SamGowland/Gowla-Macro-Boards/Images/avr.PNG

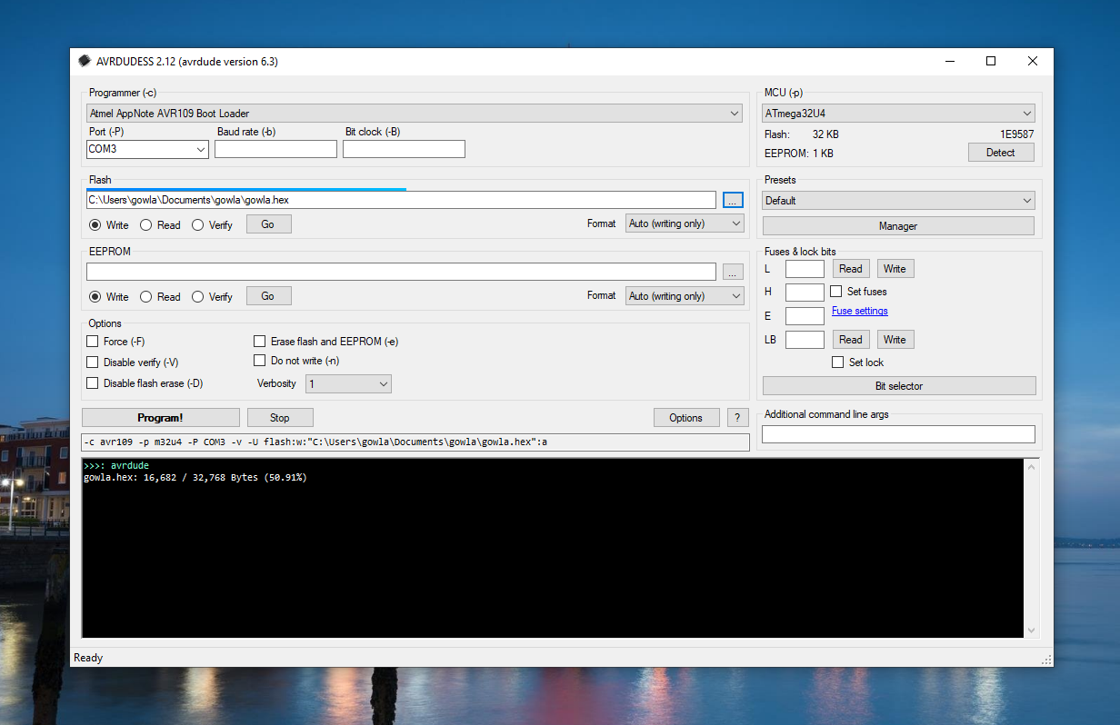
Images/avr.PNG
