SamGowland/Gowla-Macro-Boards/Images/black.PNG

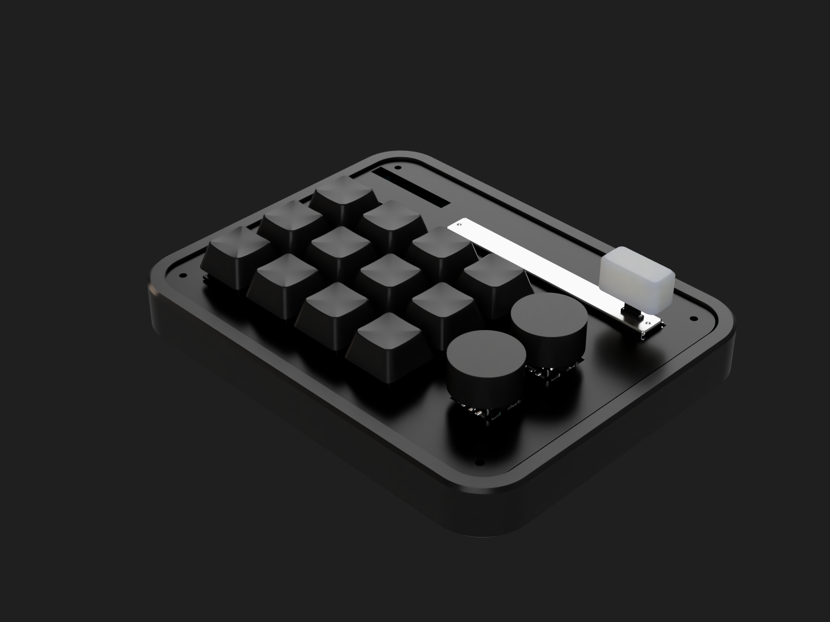
Images/black.PNG
