SamGowland/Gowla-Macro-Boards/Images/comp.jpg

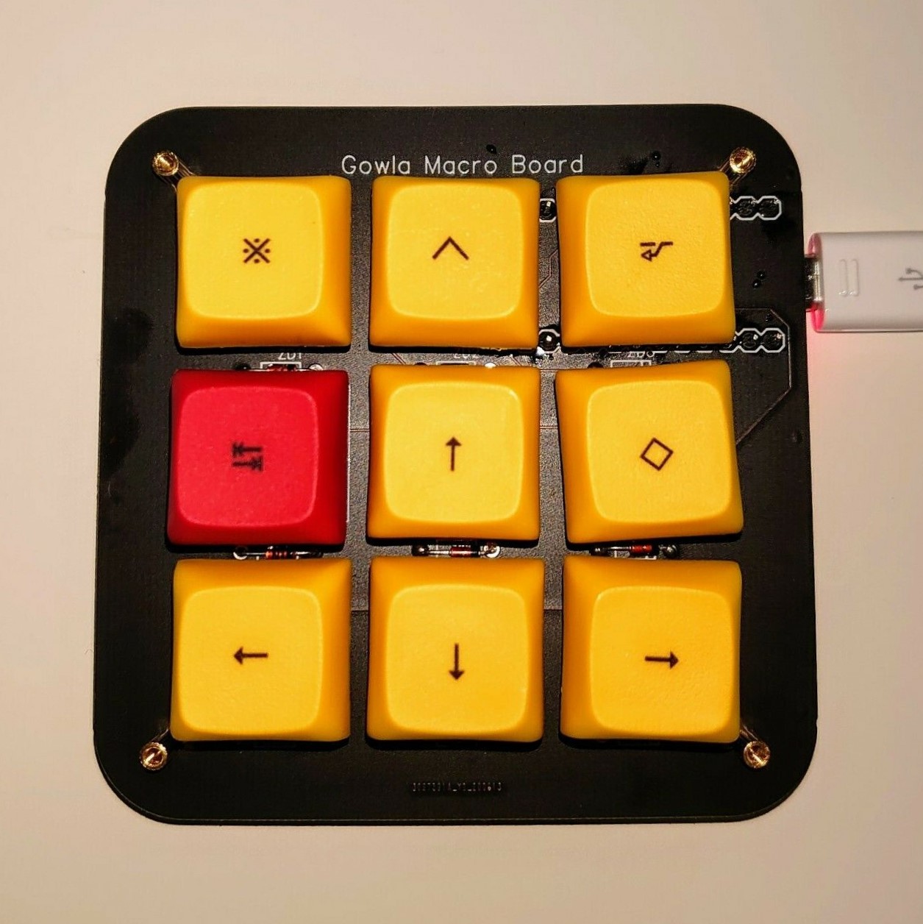
Images/comp.jpg
