SamGowland/Gowla-Macro-Boards/Images/eRGB back.PNG

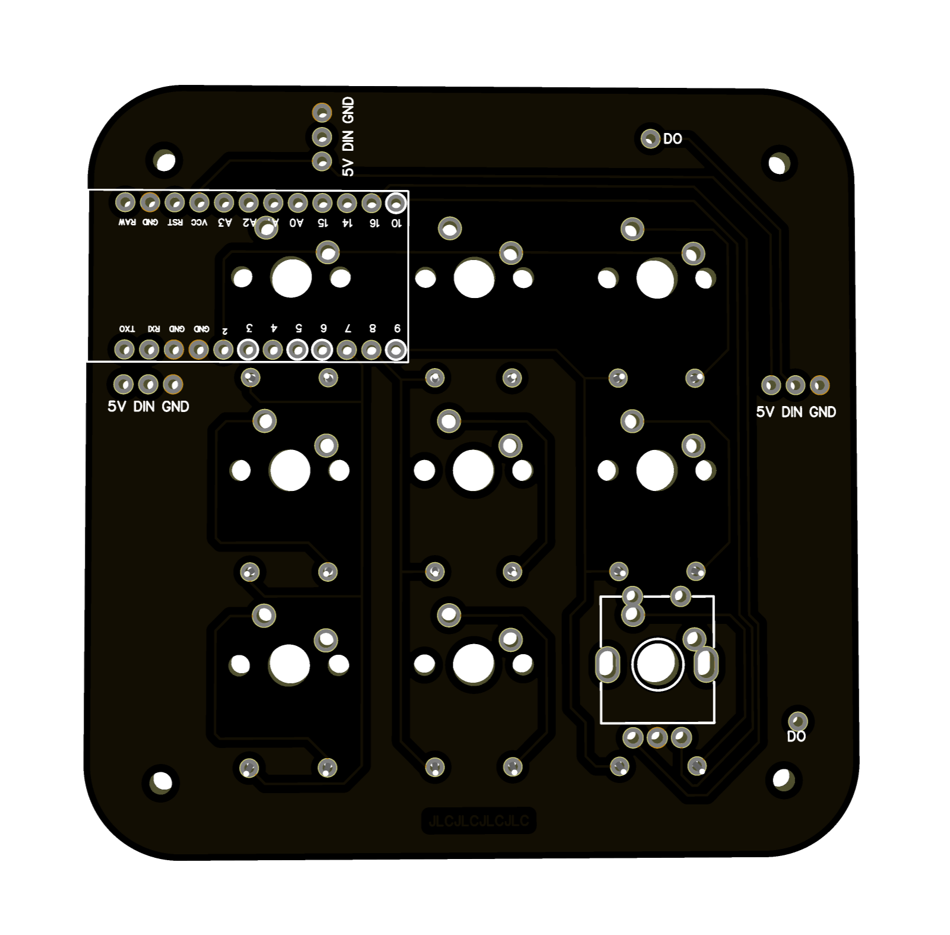
Images/eRGB back.PNG
