SamGowland/Gowla-Macro-Boards/Images/fgui.PNG

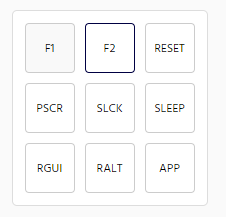
Images/fgui.PNG
