SamGowland/Gowla-Macro-Boards/Images/grgb.PNG

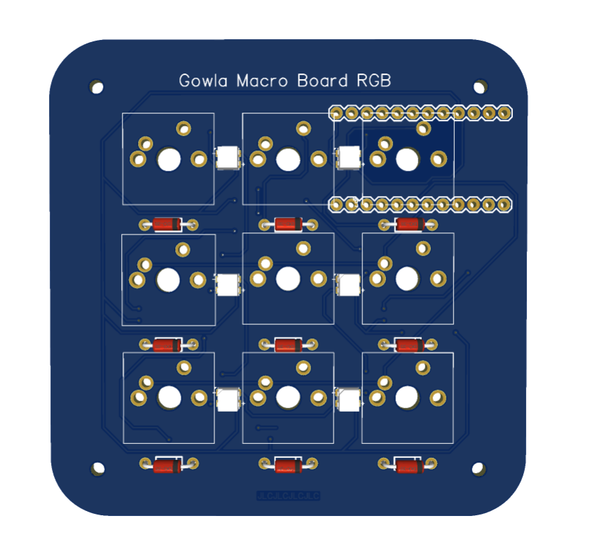
Images/grgb.PNG
