SamGowland/Gowla-Macro-Boards/Images/MEK Light Top.PNG

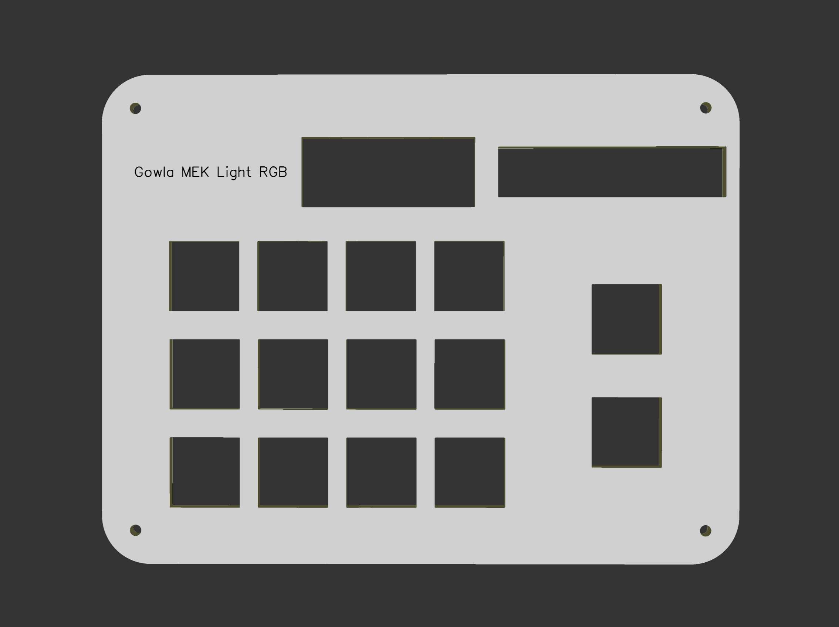
Images/MEK Light Top.PNG
