SamGowland/Gowla-Macro-Boards/Images/mek-l.PNG

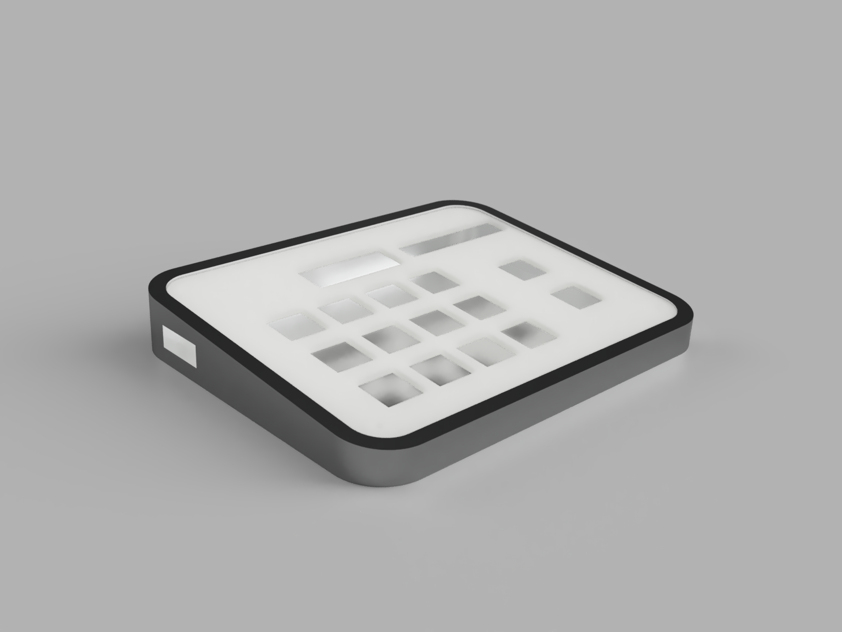
Images/mek-l.PNG
