SamGowland/Gowla-Macro-Boards/Images/nm.PNG

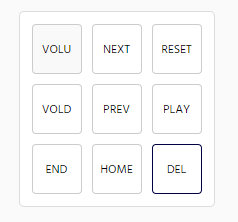
Images/nm.PNG
