SamGowland/Gowla-Macro-Boards/Images/RGB1.jpg

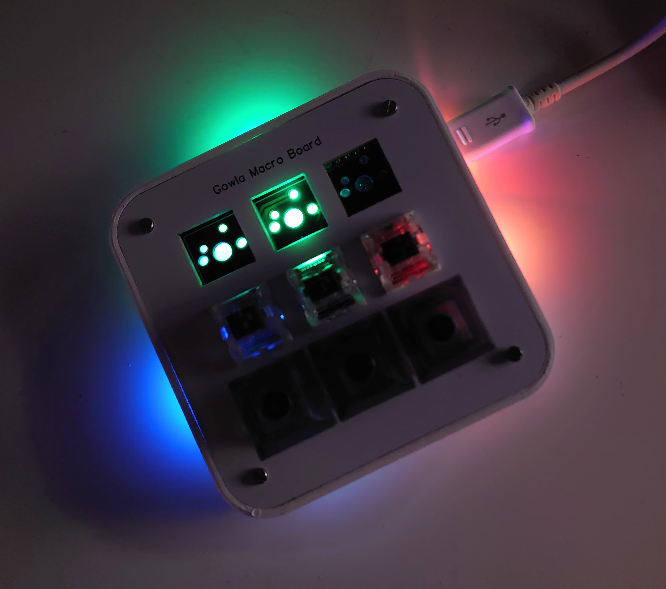
Images/RGB1.jpg
