SamGowland/Gowla-Macro-Boards/Images/RGB2.jpg

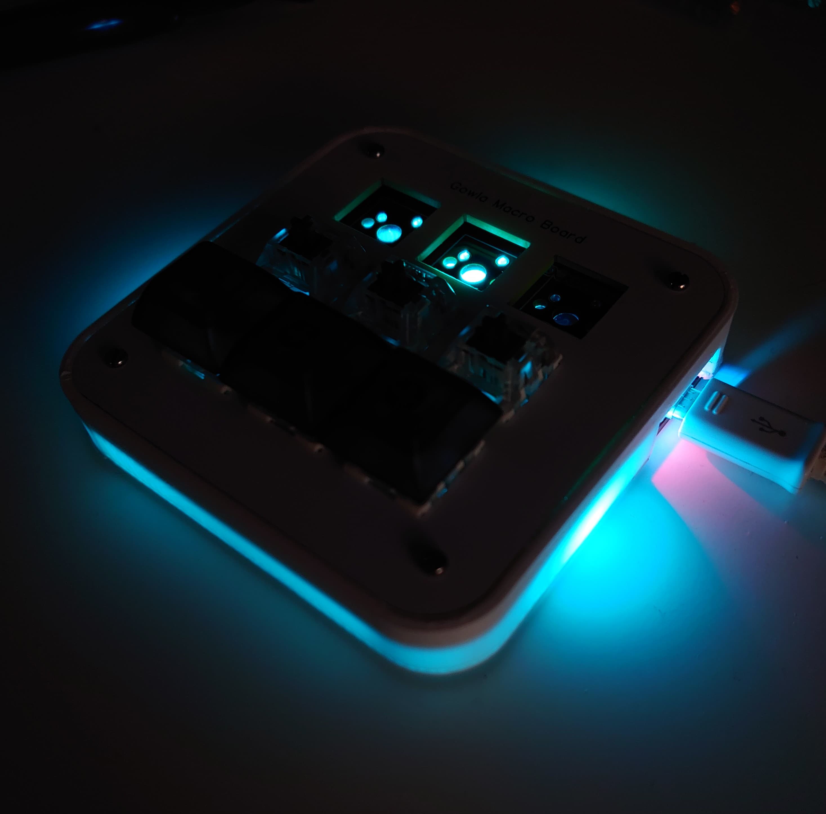
Images/RGB2.jpg
