SamGowland/Gowla-Macro-Boards/Images/tape-lit.JPG

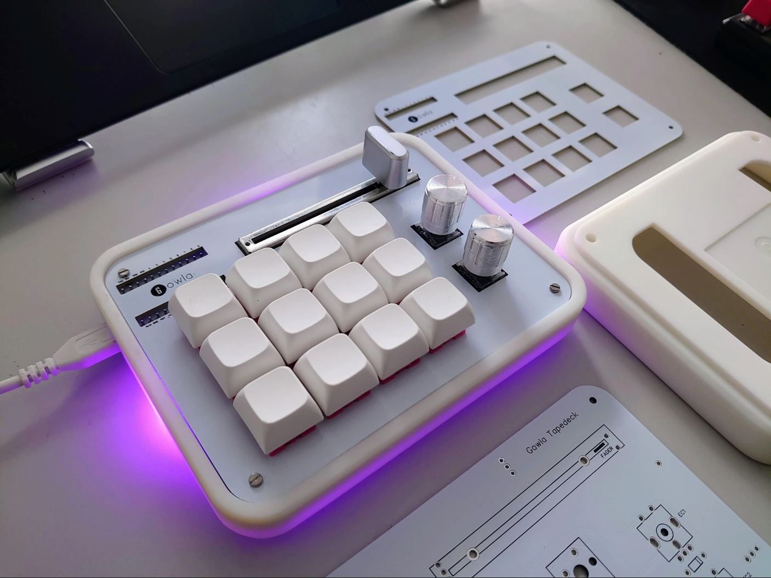
Images/tape-lit.JPG
