SamGowland/Gowla-Macro-Boards/Images/white.JPG

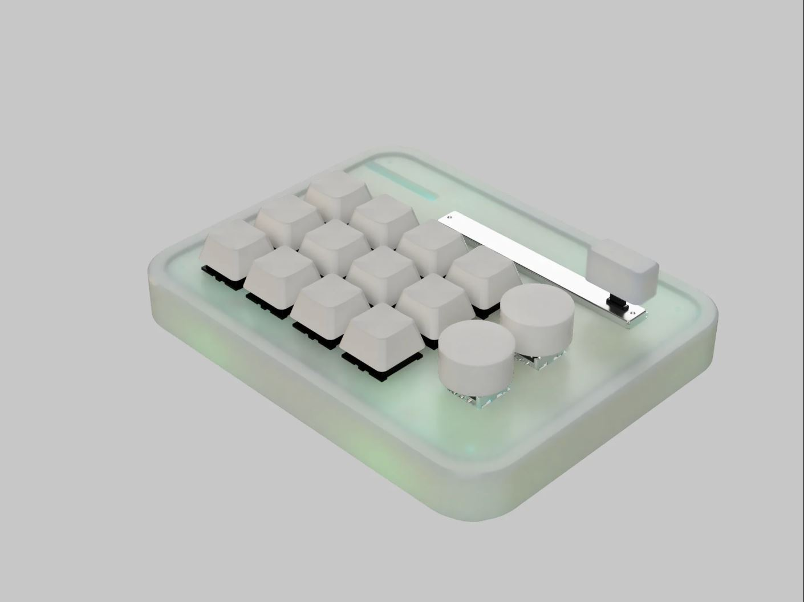
Images/white.JPG
