SamGowland/Gowla-Macro-Boards/Images/print.JPG

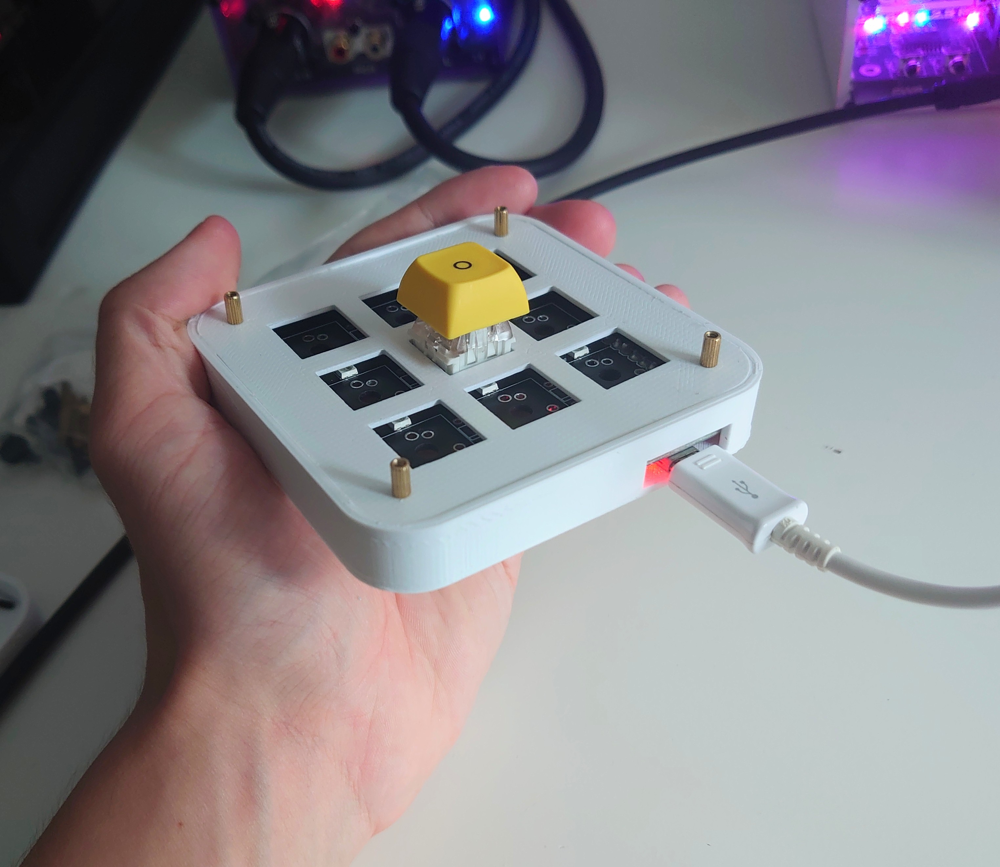
Images/print.JPG
