SamGowland/Gowla-Macro-Boards/Images/wiring.PNG

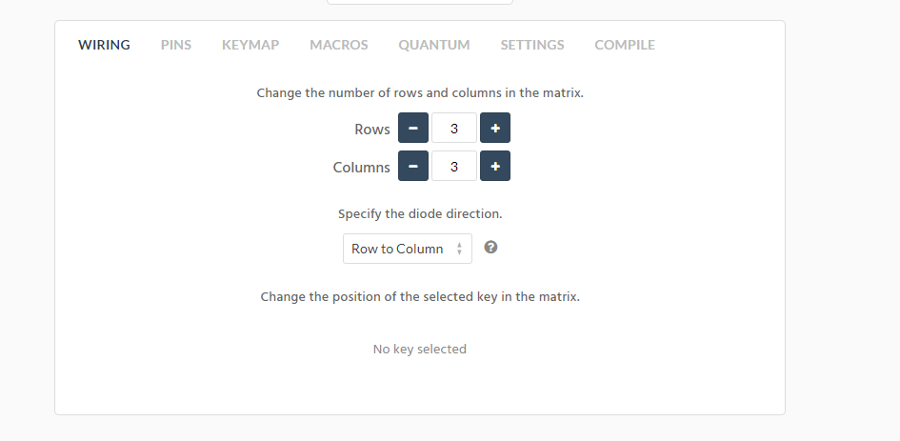
Images/wiring.PNG
